garbb/Tune2AirSucks/arduino/Tune2AirSucks/myBC127.h

#include <Arduino.h>

class MyBC127
{
  public:
    enum BC127_Status {waiting_for_boot, waiting_for_AVRCP_conn, AVRCP_connected};
    BC127_Status BC127_status;
    enum ResponseState {waiting_for_response, OK, ERR};
    ResponseState responseState;

    String responsebuffer;
    String AVRCP_linkId = "";
    String AVRCP_address = "";
    uint32_t TOstarttime;  //(time when 1st byte of reponse was received, used to detect timeout)
    const uint32_t timeoutTime = 2000; //2sec
    const String EOL = String("\n\r");  //each line of BC127 response will end in this
    Stream *_serialPort;
    #ifdef DEBUG
      Stream *myDebugSerial;
    #endif

    const String AVRCP_TITLE = "AVRCP_MEDIA TITLE: ";
    const String AVRCP_ARTIST = "AVRCP_MEDIA ARTIST: ";
    const String AVRCP_ALBUM = "AVRCP_MEDIA ALBUM: ";
    const String AVRCP_LENGTH = "AVRCP_MEDIA PLAYING_TIME(MS): ";
    
    MyBC127(Stream &sp);  //constructor
    #ifdef DEBUG
      void setdebugserial(Stream &newDebugSerial);
    #endif
    void baseSendCmd(String command);   //called by all other command sending funcs
    void SendCmd(String command);
    void SendStatusCmd();
    void MusicSendCmd(String command);

    void readResponses();
    
    void setPlaystateToStop();
    void setPlaystateToPlay();
    void setPlaystateToPause();
};

//constructor
MyBC127::MyBC127(Stream &sp)
{
  _serialPort = &sp;
  BC127_status = waiting_for_AVRCP_conn;    //###WILL INIT TO waiting_for_boot if teensy ever boots before BC127
  responseState = OK;
  responsebuffer = "";
  TOstarttime = 0;
}

#ifdef DEBUG
  void MyBC127::setdebugserial(Stream &newDebugSerial) {
    myDebugSerial = &newDebugSerial;
  }
#endif

void MyBC127::baseSendCmd(String command) {
  #ifdef DEBUG
    myDebugSerial->println(); myDebugSerial->print("<<send cmd: "); myDebugSerial->println(command);
  #endif
  _serialPort->print(command);
  _serialPort->print("\r");
}

void MyBC127::SendCmd(String command) {
  if (BC127_status == waiting_for_boot) {return;}
  baseSendCmd(command);
  responseState = waiting_for_response;
}

void MyBC127::SendStatusCmd(){
  SendCmd("STATUS");
}

void MyBC127::MusicSendCmd(String command) {
  //if (BC127_status != AVRCP_connected) {return;}  //preventing these commands are pointless, nothing happens if they fail anyways...
  baseSendCmd(command);
}

void MyBC127::readResponses() {
  if (_serialPort->available() > 0) {
    byte b = _serialPort->read();
    responsebuffer.concat(char(b));
    if (TOstarttime == 0) {TOstarttime = millis();}   //set beginning of timeout time
  }
   
  if (responsebuffer.endsWith(EOL)) {  //end of response line
    #ifdef DEBUG
      myDebugSerial->print(responsebuffer);
    #endif
    //all the response/event types
    if (responsebuffer.startsWith("OK")) {
      #ifdef DEBUG
        myDebugSerial->print(">>got OK response\n\n");
      #endif
      responseState = OK;
      }
    else if (responsebuffer.startsWith("ER")) {
      #ifdef DEBUG
        myDebugSerial->print(">>got ERROR response\n\n");
      #endif
      responseState = ERR;
      }

    else if (responsebuffer.startsWith("LINK")) {   //"status" response, displays connections
      int AVRCP_pos = responsebuffer.indexOf("AVRCP");  //position of beginning of "AVRCP" text
      if (AVRCP_pos != -1) {
        AVRCP_linkId = responsebuffer.substring(AVRCP_pos-12, AVRCP_pos-11);
        AVRCP_address = responsebuffer.substring(AVRCP_pos+6, AVRCP_pos+18);
        //read playstate from status response
        if (responsebuffer.length() >= AVRCP_pos+22) {
          String AVRCP_STATE = responsebuffer.substring(AVRCP_pos+19, AVRCP_pos+22);
          //if (AVRCP_STATE == "STO") {setPlaystateToStop();}
          if (AVRCP_STATE == "STO") {setPlaystateToPause();}
          else if (AVRCP_STATE == "PLA") {setPlaystateToPlay();}
          else if (AVRCP_STATE == "PAU") {setPlaystateToPause();}
        }
        
        #ifdef DEBUG
          myDebugSerial->print(">>AVRCP link ID is \""); myDebugSerial->print(AVRCP_linkId);
          myDebugSerial->print("\"\n>>AVRCP address is \""); myDebugSerial->print(AVRCP_address); myDebugSerial->print("\"\n");
        #endif
      }
    }
    
    else if (responsebuffer.startsWith("OPEN_OK A2DP")) {
      #ifdef DEBUG
        myDebugSerial->print(">>A2DP connected\n\n");
      #endif
      SendCmd("VOLUME A2DP=14");  //need to set this every time for volume level to sound right, it won't remember it
    }
    else if (responsebuffer.startsWith("OPEN_OK AVRCP")) {
      BC127_status = AVRCP_connected;
      #ifdef DEBUG
        myDebugSerial->print(">>AVRCP connected\n\n");
      #endif
      SendStatusCmd();    //get info about linkid and address for the AVRCP connection
    }
    else if (responsebuffer.startsWith("Ready")) {
      BC127_status = waiting_for_AVRCP_conn;
      #ifdef DEBUG
        myDebugSerial->print(">>BC127 Boot complete\n\n");
      #endif
    }
    else if (responsebuffer.startsWith("CLOSE_OK AVRCP")) {
      BC127_status = waiting_for_AVRCP_conn;
      #ifdef DEBUG
        myDebugSerial->print(">>AVRCP disconnected\n\n");
      #endif
    }
    else if (responsebuffer.startsWith("CLOSE_OK A2DP")) {
      BC127_status = waiting_for_AVRCP_conn;
      //reset track text and resend it to clear out old stuff in dock from last connection
      trackTitle = default_trackTitle;
      trackArtist = default_trackArtist;
      trackAlbum = default_trackAlbum;
      gotnewArtist = true;
      gotnewAlbum = true;
      trackchangeCmdPending = true;
      #ifdef DEBUG
        myDebugSerial->println(">>sending track changed event and new track number to ipod dock upon BT disconnnect");
        myDebugSerial->print(">>disconnected, making discoverable\n\n");
      #endif
      SendCmd("DISCOVERABLE ON");
    }

    //Ignore all AVRCP events if there is no AVRCP connection (sometimes we randomly get AVRCP_PLAY before connection even if actual playing state is paused)
    //I don't understand if this is a bug or what but lets just ignore them.
    else if (BC127_status == AVRCP_connected) {
      
      if (responsebuffer.startsWith(AVRCP_TITLE)) {
        //store last track title
        last_trackTitle = trackTitle;
        //store new title
        trackTitle = (responsebuffer.substring(AVRCP_TITLE.length())).trim();

        //am going to set play state to PLAYING here b/c in some random cases when switching between android apps while playing music will get AVRCP_PAUSE event
        //even though music is actually playing. AFAICT, when we get AVRCP_TITLE event, play state is always playing (EXCEPT UPON INITIAL CONNECTION).
//        playingState = STATE_PLAYING;
//        trackstarttime = now;
//        #ifdef DEBUG
//          myDebugSerial->print(">>play state changed to "); myDebugSerial->print(playingState); myDebugSerial->print("\n\n");
//        #endif
        trackchangeCmdPending = true;
        albumartistWaitstart = now;
      }
      else if (responsebuffer.startsWith(AVRCP_ARTIST)) {
        //store last Artist
        last_trackArtist = trackArtist;
        //store new Artist
        trackArtist = (responsebuffer.substring(AVRCP_ARTIST.length())).trim();
        gotnewArtist = true;
      }
      else if (responsebuffer.startsWith(AVRCP_ALBUM)) {
        //store last Album
        last_trackAlbum = trackAlbum;
        //store new Album
        trackAlbum = (responsebuffer.substring(AVRCP_ALBUM.length())).trim();
        gotnewAlbum = true;
      }
      else if (responsebuffer.startsWith(AVRCP_LENGTH)) {
        trackLength = (responsebuffer.substring(AVRCP_LENGTH.length())).toInt();
        //some apps (spotify) output track length as sec instead of ms
        //we will just assume that if we get a small number then it is in sec instead of ms
        if (trackLength < 1000) {trackLength *= 1000;}
        #ifdef DEBUG
          myDebugSerial->print(">>LENGTH IS: \""); myDebugSerial->print(trackLength); myDebugSerial->println("ms\"");
        #endif
      }
  
      else if (responsebuffer.startsWith("AVRCP_STOP")) { //this never seems to happen with android apps I tested but might happen with something??
        //setPlaystateToStop();
        setPlaystateToPause();
        //timer to run BC127 status command after playstate event is received to check "real" playstate
        timer.setTimeout(1000, SendStatusCmd_t);
      }
      else if (responsebuffer.startsWith("AVRCP_PLAY")) {
        setPlaystateToPlay();
        timer.setTimeout(1000, SendStatusCmd_t);
      }
      else if (responsebuffer.startsWith("AVRCP_PAUSE")) {
        setPlaystateToPause();
        timer.setTimeout(1000, SendStatusCmd_t);
      }

    }
//    if (prevplayingState != playingState) {allowPlayPausecmd = true;}
//    prevplayingState = playingState;
    
    responsebuffer = "";
    TOstarttime = 0;
  }

  //timeout handling
  if ( (TOstarttime > 0) && (millis() - TOstarttime) > timeoutTime ) {
    #ifdef DEBUG
      myDebugSerial->print(">>response EOL timeout"); myDebugSerial->print("\n\n");
    #endif
    responseState = ERR;
    responsebuffer = "";
    TOstarttime = 0;
  }
}

void MyBC127::setPlaystateToStop() {
  if (playingState != STATE_PAUSED && playingState != STATE_STOPPED) accumTrackPlaytime += now - trackstarttime;  //add track playing time when we pause/stop?
  playingState = STATE_STOPPED;
  #ifdef DEBUG
    myDebugSerial->print(now); myDebugSerial->print(">>play state changed to "); myDebugSerial->print(playingState); myDebugSerial->print("\n\n");
  #endif
}

void MyBC127::setPlaystateToPlay() {
  if (playingState != STATE_PLAYING) trackstarttime = now;
  playingState = STATE_PLAYING;
  #ifdef DEBUG
    myDebugSerial->print(now); myDebugSerial->print(">>play state changed to "); myDebugSerial->print(playingState); myDebugSerial->print("\n\n");
  #endif
}

void MyBC127::setPlaystateToPause() {
  if (playingState != STATE_PAUSED && playingState != STATE_STOPPED) {   //don't add more to accum time if we are already paused
    accumTrackPlaytime += now - trackstarttime;  //add track playing time when we pause
  }
  playingState = STATE_PAUSED;
  #ifdef DEBUG
    myDebugSerial->print(now); myDebugSerial->print(">>play state changed to "); myDebugSerial->print(playingState); myDebugSerial->print("\n\n");
  #endif
}
